cdierk/HairIO/hair_input_output_bluetooth/hair_input_output_bluetooth.ino

/*Copyright (c) 2010 bildr community

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
 THE SOFTWARE IS PROVIDED "AS IS", WITHOUT WARRANTY OF ANY KIND, EXPRESS OR
 IMPLIED, INCLUDING BUT NOT LIMITED TO THE WARRANTIES OF MERCHANTABILITY,
 FITNESS FOR A PARTICULAR PURPOSE AND NONINFRINGEMENT. IN NO EVENT SHALL THE
 AUTHORS OR COPYRIGHT HOLDERS BE LIABLE FOR ANY CLAIM, DAMAGES OR OTHER
 LIABILITY, WHETHER IN AN ACTION OF CONTRACT, TORT OR OTHERWISE, ARISING FROM,
 OUT OF OR IN CONNECTION WITH THE SOFTWARE OR THE USE OR OTHER DEALINGS IN
 THE SOFTWARE.
*/

#include "mpr121.h"
#include <Wire.h>

#include <Arduino.h>
#include <SPI.h>
#if not defined (_VARIANT_ARDUINO_DUE_X_) && not defined (_VARIANT_ARDUINO_ZERO_)
  #include <SoftwareSerial.h>
#endif

#include "Adafruit_BLE.h"
#include "Adafruit_BluefruitLE_UART.h"

#include "BluefruitConfig.h"

#define FACTORYRESET_ENABLE         1
#define MINIMUM_FIRMWARE_VERSION    "0.6.6"
#define MODE_LED_BEHAVIOUR          "MODE"

int irqpin = 2;  // Digital 2
boolean touchStates[12]; //to keep track of the previous touch states

const int ledPin =  13;

SoftwareSerial bluefruitSS = SoftwareSerial(BLUEFRUIT_SWUART_TXD_PIN, BLUEFRUIT_SWUART_RXD_PIN);

Adafruit_BluefruitLE_UART ble(bluefruitSS, BLUEFRUIT_UART_MODE_PIN,
                      BLUEFRUIT_UART_CTS_PIN, BLUEFRUIT_UART_RTS_PIN);


// A small helper
void error(const __FlashStringHelper*err) {
  Serial.println(err);
  while (1);
}

void setup(){
  pinMode(irqpin, INPUT);
  pinMode(4, OUTPUT);
  digitalWrite(irqpin, HIGH); //enable pullup resistor

  while (!Serial);  // required for Flora & Micro
  delay(500);
  
  Serial.begin(115200);
  Wire.begin();

  mpr121_setup();

  pinMode(ledPin, OUTPUT);

  Serial.println(F("Adafruit Bluefruit Command <-> Data Mode Example"));
  Serial.println(F("------------------------------------------------"));

  /* Initialise the module */
  Serial.print(F("Initialising the Bluefruit LE module: "));

  if ( !ble.begin(VERBOSE_MODE) )
  {
    error(F("Couldn't find Bluefruit, make sure it's in CoMmanD mode & check wiring?"));
  }
  Serial.println( F("OK!") );

  if ( FACTORYRESET_ENABLE )
  {
    /* Perform a factory reset to make sure everything is in a known state */
    Serial.println(F("Performing a factory reset: "));
    if ( ! ble.factoryReset() ){
      error(F("Couldn't factory reset"));
    }
  }

  /* Disable command echo from Bluefruit */
  ble.echo(false);

  Serial.println("Requesting Bluefruit info:");
  /* Print Bluefruit information */
  ble.info();

  Serial.println(F("Please use Adafruit Bluefruit LE app to connect in UART mode"));
  Serial.println(F("Then Enter characters to send to Bluefruit"));
  Serial.println();

  ble.verbose(false);  // debug info is a little annoying after this point!

  /* Wait for connection */
  while (! ble.isConnected()) {
      delay(500);
  }

  Serial.println(F("******************************"));

  // LED Activity command is only supported from 0.6.6
  if ( ble.isVersionAtLeast(MINIMUM_FIRMWARE_VERSION) )
  {
    // Change Mode LED Activity
    Serial.println(F("Change LED activity to " MODE_LED_BEHAVIOUR));
    ble.sendCommandCheckOK("AT+HWModeLED=" MODE_LED_BEHAVIOUR);
  }

  // Set module to DATA mode
  Serial.println( F("Switching to DATA mode!") );
  ble.setMode(BLUEFRUIT_MODE_DATA);

  Serial.println(F("******************************"));
}

void loop(){
  readTouchInputs();

  String received = "";
  
  // Echo received data
  while ( ble.available() )
  {
    int c = ble.read();
    received = received + (char) c;
    //Serial.println((char)c);
    //Serial.println(received);
    if (received.equals("!B10;")){
      digitalWrite(4,HIGH);
    } else if (received.equals("!B219")){
      digitalWrite(4,LOW);
    }
  }
}


void readTouchInputs(){
  if(!checkInterrupt()){
    
    //read the touch state from the MPR121
    Wire.requestFrom(0x5A,2); 
    
    byte LSB = Wire.read();
    byte MSB = Wire.read();
    
    uint16_t touched = ((MSB << 8) | LSB); //16bits that make up the touch states

    
    for (int i=0; i < 12; i++){  // Check what electrodes were pressed
      if(touched & (1<<i)){
      
        if(touchStates[i] == 0){
          //pin i was just touched
          Serial.print("pin ");
          Serial.print(i);
          Serial.println(" was just touched");
          digitalWrite(ledPin, HIGH);

          String s = "braid touched                                       ";
          uint8_t sendbuffer[20];
          s.getBytes(sendbuffer, 20);
          char sendbuffersize = min(20, s.length());

          Serial.print(F("\n* Sending -> \"")); Serial.print((char *)sendbuffer); Serial.println("\"");

          ble.write(sendbuffer, sendbuffersize);
        
        }else if(touchStates[i] == 1){
          //pin i is still being touched
        }  
      
        touchStates[i] = 1;      
      }else{
        if(touchStates[i] == 1){
          Serial.print("pin ");
          Serial.print(i);
          Serial.println(" is no longer being touched");
          digitalWrite(ledPin, LOW);
          
          //pin i is no longer being touched
       }
        
        touchStates[i] = 0;
      }
    
    }
    
  }
}




void mpr121_setup(void){

  set_register(0x5A, ELE_CFG, 0x00); 
  
  // Section A - Controls filtering when data is > baseline.
  set_register(0x5A, MHD_R, 0x01);
  set_register(0x5A, NHD_R, 0x01);
  set_register(0x5A, NCL_R, 0x00);
  set_register(0x5A, FDL_R, 0x00);

  // Section B - Controls filtering when data is < baseline.
  set_register(0x5A, MHD_F, 0x01);
  set_register(0x5A, NHD_F, 0x01);
  set_register(0x5A, NCL_F, 0xFF);
  set_register(0x5A, FDL_F, 0x02);
  
  // Section C - Sets touch and release thresholds for each electrode
  set_register(0x5A, ELE0_T, TOU_THRESH);
  set_register(0x5A, ELE0_R, REL_THRESH);
 
  set_register(0x5A, ELE1_T, TOU_THRESH);
  set_register(0x5A, ELE1_R, REL_THRESH);
  
  set_register(0x5A, ELE2_T, TOU_THRESH);
  set_register(0x5A, ELE2_R, REL_THRESH);
  
  set_register(0x5A, ELE3_T, TOU_THRESH);
  set_register(0x5A, ELE3_R, REL_THRESH);
  
  set_register(0x5A, ELE4_T, TOU_THRESH);
  set_register(0x5A, ELE4_R, REL_THRESH);
  
  set_register(0x5A, ELE5_T, TOU_THRESH);
  set_register(0x5A, ELE5_R, REL_THRESH);
  
  set_register(0x5A, ELE6_T, TOU_THRESH);
  set_register(0x5A, ELE6_R, REL_THRESH);
  
  set_register(0x5A, ELE7_T, TOU_THRESH);
  set_register(0x5A, ELE7_R, REL_THRESH);
  
  set_register(0x5A, ELE8_T, TOU_THRESH);
  set_register(0x5A, ELE8_R, REL_THRESH);
  
  set_register(0x5A, ELE9_T, TOU_THRESH);
  set_register(0x5A, ELE9_R, REL_THRESH);
  
  set_register(0x5A, ELE10_T, TOU_THRESH);
  set_register(0x5A, ELE10_R, REL_THRESH);
  
  set_register(0x5A, ELE11_T, TOU_THRESH);
  set_register(0x5A, ELE11_R, REL_THRESH);
  
  // Section D
  // Set the Filter Configuration
  // Set ESI2
  set_register(0x5A, FIL_CFG, 0x04);
  
  // Section E
  // Electrode Configuration
  // Set ELE_CFG to 0x00 to return to standby mode
  set_register(0x5A, ELE_CFG, 0x0C);  // Enables all 12 Electrodes
  
  
  // Section F
  // Enable Auto Config and auto Reconfig
  /*set_register(0x5A, ATO_CFG0, 0x0B);
  set_register(0x5A, ATO_CFGU, 0xC9);  // USL = (Vdd-0.7)/vdd*256 = 0xC9 @3.3V   set_register(0x5A, ATO_CFGL, 0x82);  // LSL = 0.65*USL = 0x82 @3.3V
  set_register(0x5A, ATO_CFGT, 0xB5);*/  // Target = 0.9*USL = 0xB5 @3.3V
  
  set_register(0x5A, ELE_CFG, 0x0C);
  
}


boolean checkInterrupt(void){
  return digitalRead(irqpin);
}


void set_register(int address, unsigned char r, unsigned char v){
    Wire.beginTransmission(address);
    Wire.write(r);
    Wire.write(v);
    Wire.endTransmission();
}
